guilhermefernandesk/Projeto-Placa-PBLE02/Codigo.X/stateMachine.h

/* 
 * File:   stateMachine.h
 * Author: Avell
 *
 * Created on 18 de Junho de 2017, 22:17
 */

#ifndef STATEMACHINE_H
#define	STATEMACHINE_H


//estados da maquina de Estados

enum {
    STATE_ALARME_TEMP_MAX,
    STATE_ALARME_PRESS_MAX, 
    STATE_ALARME_TEMP_MIN,
    STATE_ALARME_PRESS_MIN, 
    STATE_TEMPO,
    STATE_IDIOMA,
    STATE_FIM
};


void smInit(void);
void smLoop(void);


#endif	/* STATEMACHINE_H */
