guilhermefernandesk/Projeto-Placa-PBLE02/Codigo.X/config.h

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

#ifndef CONFIG_H
#define CONFIG_H

#define PIC18F4550
//#define PIC18F4520

#ifdef PIC18F4550
//configurações do microcontrolador
#pragma config MCLRE=ON                // Master Clear desabilitado
#pragma config FOSC=HS                 // Oscilador c/ cristal externo HS
#pragma config WDT=OFF                 // Watchdog controlado por software
#pragma config LVP=OFF                 // Sem programação em baixa tensão
#pragma config ICPRT=ON
#pragma config CCP2MX = OFF
#endif

#ifdef PIC18F4520
    #pragma config MCLRE=ON                // Master Clear desabilitado
    #pragma config OSC=HS                  // Oscilador c/ cristal externo HS
    #pragma config WDT=OFF                 // Watchdog controlado por software
    #pragma config LVP=OFF                 // Sem programação em baixa tensão
    #pragma config DEBUG = OFF             // Desabilita debug
    #pragma config WDTPS = 1               // Configura prescaler do watchdog
#endif

#endif
