guilhermefernandesk/Projeto-Placa-PBLE02/Codigo.X/serial.c

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
#include "serial.h"
#include "pic18f4520.h"

void serialInit(void) {
    TXSTA = 0b00101100; //configura a transmissão de dados da serial
    RCSTA = 0b10010000; //configura a recepção de dados da serial
    BAUDCON = 0b00001000; //configura sistema de velocidade da serial
    SPBRGH = 0b00000000; //configura para 56k
    SPBRG = 0b00100010; //configura para 56k
    BitSet(TRISC, 6); //pino de recepção de dados
    BitSet(TRISC, 7); //pino de envio de dados
}

//Envia dados para o Serial
void serialSend(unsigned char c) {
    
    while (!BitTst(PIR1, 4)); //aguarda o registro ficar disponível
    TXREG = c; //coloca o valor para ser enviado
}
 
//Le dados do Serial
unsigned char serialRead(void) {
   
    char resp = 0;

    if (BitTst(RCSTA, 1)) //Verifica se há erro de overrun e reseta a serial
    {
        BitClr(RCSTA, 4);
        BitSet(RCSTA, 4);
    }

    if (BitTst(PIR1, 5)) //Verifica se existe algum valor disponivel
    {
        resp = RCREG; //retorna o valor
    }
    return resp; //retorna zero


}

//Envia um número inteiro para o Serial

void serialInt(int val) {
    if (val < 0) {
        val = val * (-1);
        serialSend('-');
    }
    serialSend((val / 10000) % 10 + 48);
    serialSend((val / 1000) % 10 + 48);
    serialSend((val / 100) % 10 + 48);
    serialSend((val / 10) % 10 + 48);
    serialSend((val / 1) % 10 + 48);

}

//Envia uma string para o Serial

void serialString(const char *str){
    while (*str) {
        serialSend(*str++);
    }
}
